CedarGroveStudios/Clock_MiniM4_Pelican/PCB/Clock_MiniM4_Pelican_bot.png

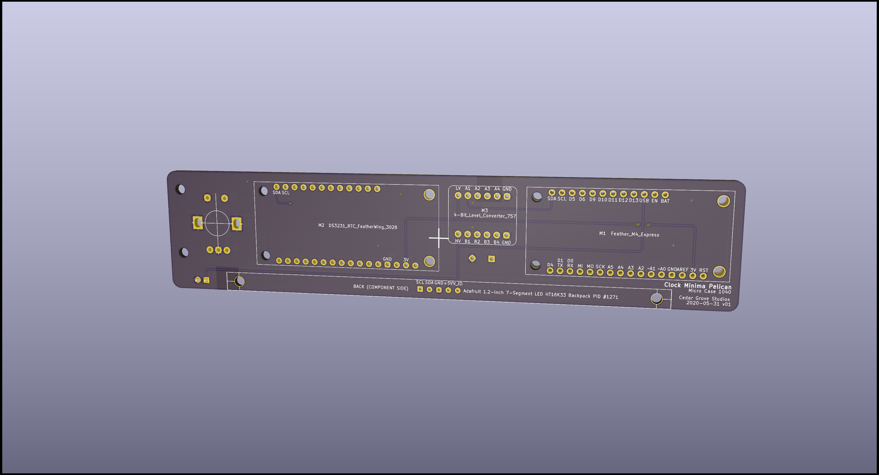
PCB/Clock_MiniM4_Pelican_bot.png
