CedarGroveStudios/Clock_MiniM4_Pelican/photos and graphics/IMG_0286.jpeg

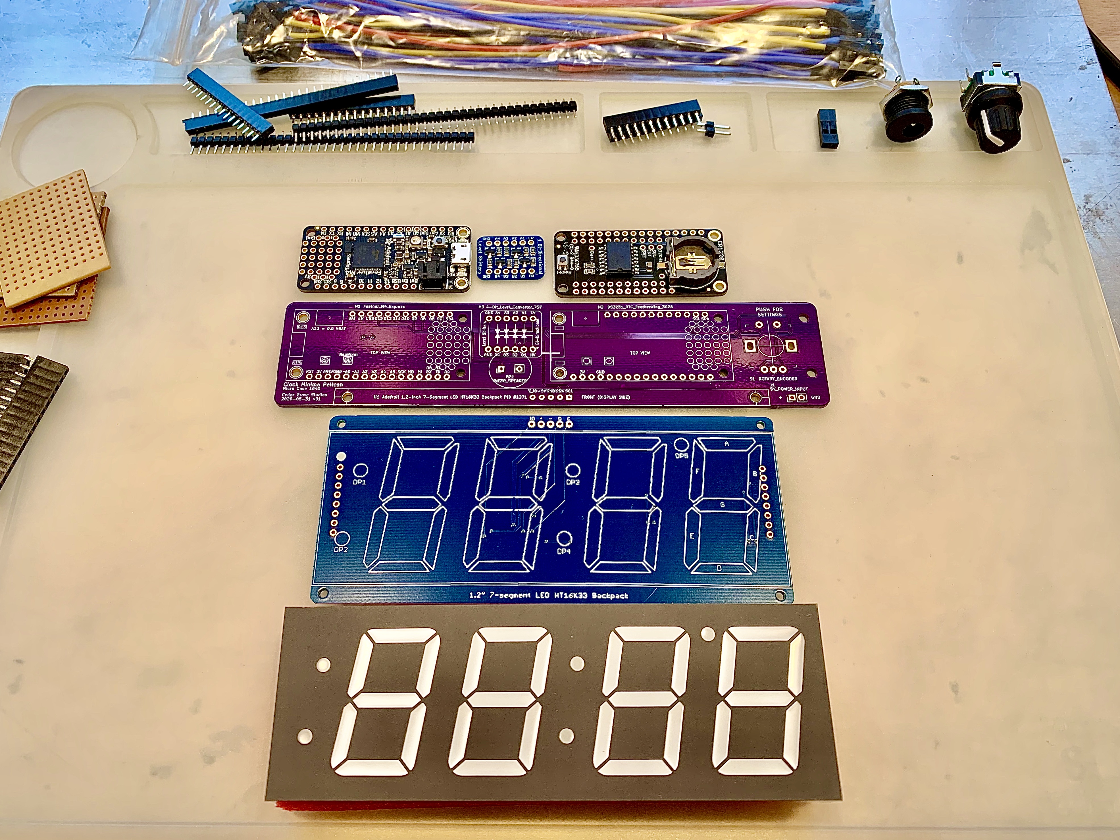
photos and graphics/IMG_0286.jpeg
