CedarGroveStudios/Clock_MiniM4_Pelican/photos and graphics/IMG_0289.jpeg

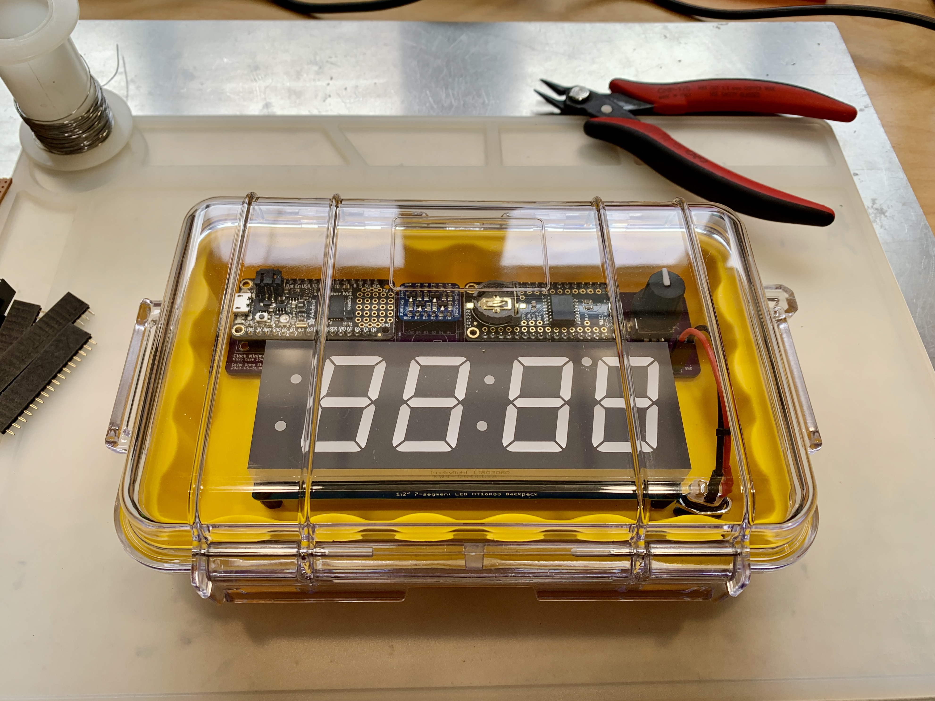
photos and graphics/IMG_0289.jpeg
