CedarGroveStudios/Clock_MiniM4_Pelican/photos and graphics/IMG_0290.jpeg

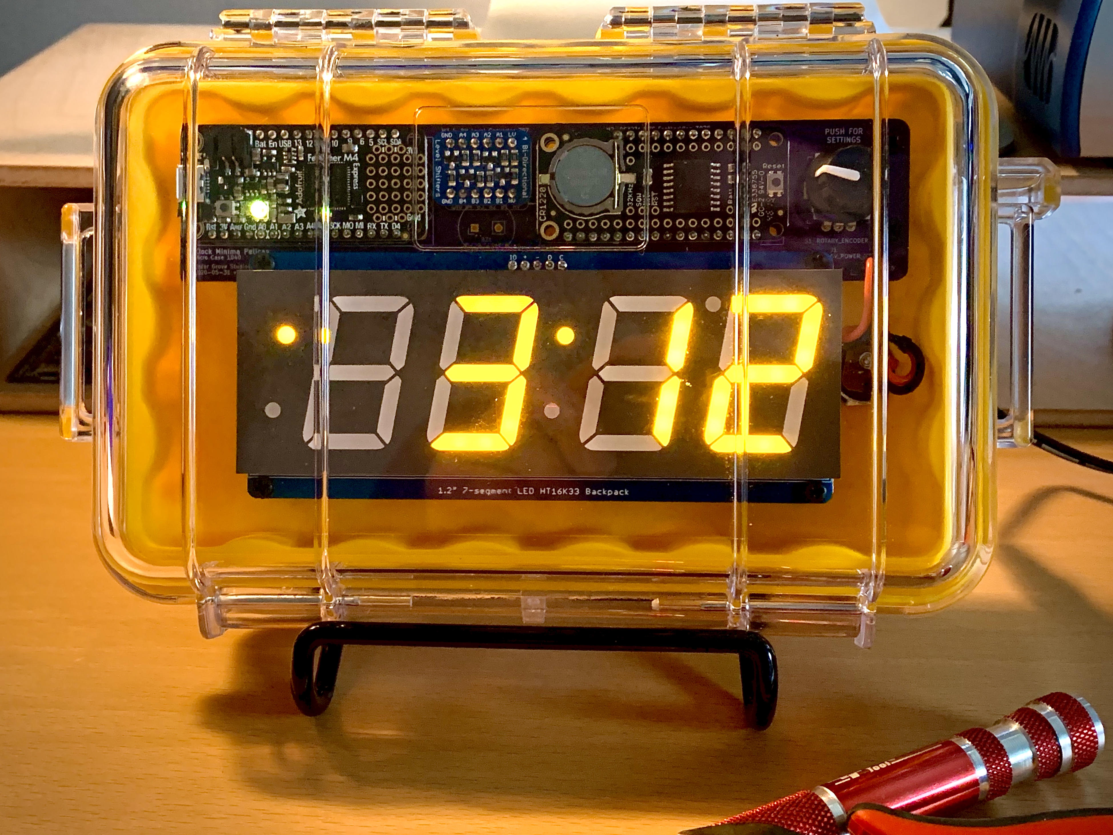
photos and graphics/IMG_0290.jpeg
