CedarGroveStudios/Clock_MiniM4_Pelican/photos and graphics/IMG_0297.jpeg

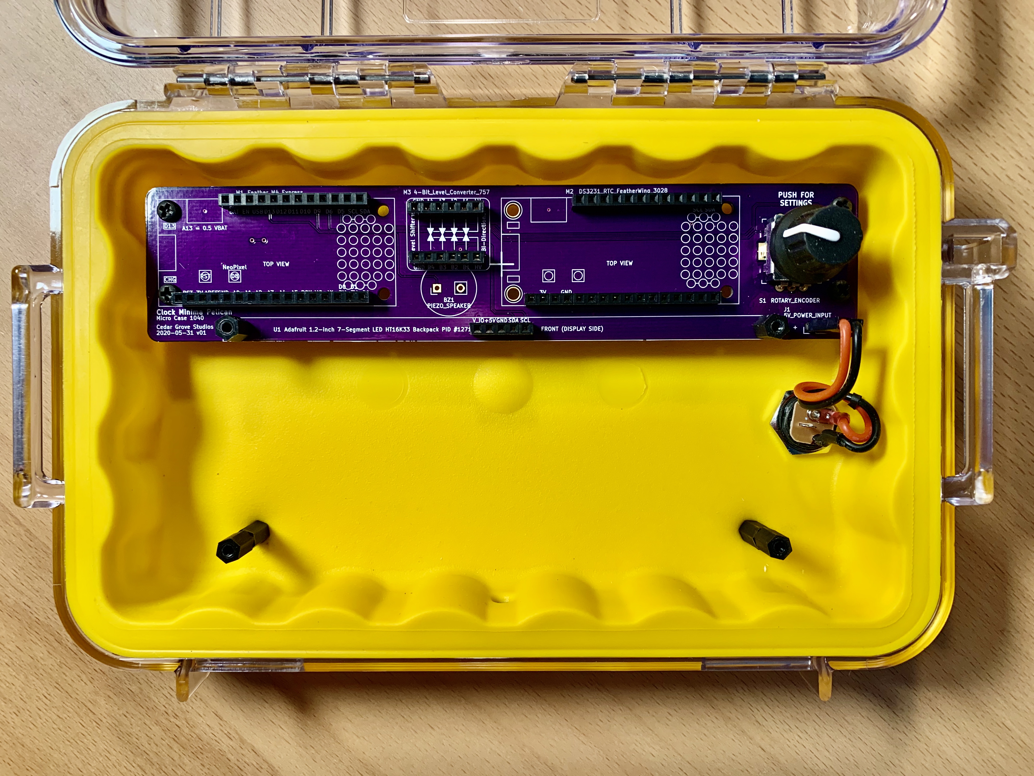
photos and graphics/IMG_0297.jpeg
