CedarGroveStudios/Clock_MiniM4_Pelican/photos and graphics/IMG_0298.jpeg

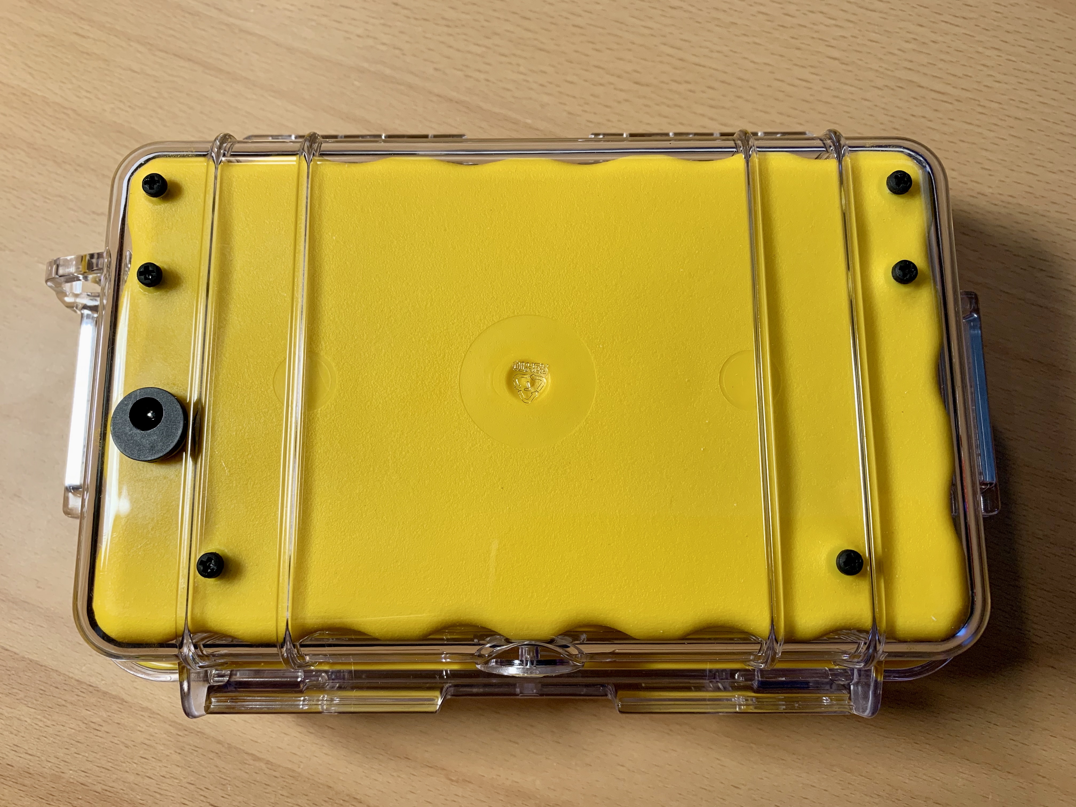
photos and graphics/IMG_0298.jpeg
